NoahPerkovich/pi-pico-mag/operate/sdcard.py

"""
MicroPython driver for SD cards using SPI bus.

Requires an SPI bus and a CS pin.  Provides readblocks and writeblocks
methods so the device can be mounted as a filesystem.

Example usage on pyboard:

    import pyb, sdcard, os
    sd = sdcard.SDCard(pyb.SPI(1), pyb.Pin.board.X5)
    pyb.mount(sd, '/sd2')
    os.listdir('/')

Example usage on ESP8266:

    import machine, sdcard, os
    sd = sdcard.SDCard(machine.SPI(1), machine.Pin(15))
    os.mount(sd, '/sd')
    os.listdir('/')

"""

import micropython
from micropython import const
import time
import uctypes

import array

crc7_be_syndrome_table = array.array("B", 0 for x in range(256)) #pre-allocate so it is low in memory

for i, x in enumerate([
	0x00, 0x12, 0x24, 0x36, 0x48, 0x5a, 0x6c, 0x7e,
	0x90, 0x82, 0xb4, 0xa6, 0xd8, 0xca, 0xfc, 0xee,
	0x32, 0x20, 0x16, 0x04, 0x7a, 0x68, 0x5e, 0x4c,
	0xa2, 0xb0, 0x86, 0x94, 0xea, 0xf8, 0xce, 0xdc,
	0x64, 0x76, 0x40, 0x52, 0x2c, 0x3e, 0x08, 0x1a,
	0xf4, 0xe6, 0xd0, 0xc2, 0xbc, 0xae, 0x98, 0x8a,
	0x56, 0x44, 0x72, 0x60, 0x1e, 0x0c, 0x3a, 0x28,
	0xc6, 0xd4, 0xe2, 0xf0, 0x8e, 0x9c, 0xaa, 0xb8,
	0xc8, 0xda, 0xec, 0xfe, 0x80, 0x92, 0xa4, 0xb6,
	0x58, 0x4a, 0x7c, 0x6e, 0x10, 0x02, 0x34, 0x26,
	0xfa, 0xe8, 0xde, 0xcc, 0xb2, 0xa0, 0x96, 0x84,
	0x6a, 0x78, 0x4e, 0x5c, 0x22, 0x30, 0x06, 0x14,
	0xac, 0xbe, 0x88, 0x9a, 0xe4, 0xf6, 0xc0, 0xd2,
	0x3c, 0x2e, 0x18, 0x0a, 0x74, 0x66, 0x50, 0x42,
	0x9e, 0x8c, 0xba, 0xa8, 0xd6, 0xc4, 0xf2, 0xe0,
	0x0e, 0x1c, 0x2a, 0x38, 0x46, 0x54, 0x62, 0x70,
	0x82, 0x90, 0xa6, 0xb4, 0xca, 0xd8, 0xee, 0xfc,
	0x12, 0x00, 0x36, 0x24, 0x5a, 0x48, 0x7e, 0x6c,
	0xb0, 0xa2, 0x94, 0x86, 0xf8, 0xea, 0xdc, 0xce,
	0x20, 0x32, 0x04, 0x16, 0x68, 0x7a, 0x4c, 0x5e,
	0xe6, 0xf4, 0xc2, 0xd0, 0xae, 0xbc, 0x8a, 0x98,
	0x76, 0x64, 0x52, 0x40, 0x3e, 0x2c, 0x1a, 0x08,
	0xd4, 0xc6, 0xf0, 0xe2, 0x9c, 0x8e, 0xb8, 0xaa,
	0x44, 0x56, 0x60, 0x72, 0x0c, 0x1e, 0x28, 0x3a,
	0x4a, 0x58, 0x6e, 0x7c, 0x02, 0x10, 0x26, 0x34,
	0xda, 0xc8, 0xfe, 0xec, 0x92, 0x80, 0xb6, 0xa4,
	0x78, 0x6a, 0x5c, 0x4e, 0x30, 0x22, 0x14, 0x06,
	0xe8, 0xfa, 0xcc, 0xde, 0xa0, 0xb2, 0x84, 0x96,
	0x2e, 0x3c, 0x0a, 0x18, 0x66, 0x74, 0x42, 0x50,
	0xbe, 0xac, 0x9a, 0x88, 0xf6, 0xe4, 0xd2, 0xc0,
	0x1c, 0x0e, 0x38, 0x2a, 0x54, 0x46, 0x70, 0x62,
	0x8c, 0x9e, 0xa8, 0xba, 0xc4, 0xd6, 0xe0, 0xf2
]):
    crc7_be_syndrome_table[i] = x #fill pre-allocated table


import gc
gc.collect() #make sure residual list gets cleaned up to save memory

@micropython.viper
def crc7(buf, n:int) -> int:
    table = ptr8(uctypes.addressof(crc7_be_syndrome_table))
    bp = ptr8(uctypes.addressof(buf))
    idx = 0
    crc = 0
    while idx < n:
        crc = table[crc ^ bp[idx]]
        idx  = idx + 1  
    return crc

_CMD_TIMEOUT = const(50)

_R1_IDLE_STATE = const(1 << 0)
# R1_ERASE_RESET = const(1 << 1)
_R1_ILLEGAL_COMMAND = const(1 << 2)
# R1_COM_CRC_ERROR = const(1 << 3)
# R1_ERASE_SEQUENCE_ERROR = const(1 << 4)
# R1_ADDRESS_ERROR = const(1 << 5)
# R1_PARAMETER_ERROR = const(1 << 6)
_TOKEN_CMD25 = const(0xFC)
_TOKEN_STOP_TRAN = const(0xFD)
_TOKEN_DATA = const(0xFE)


class SDCard:
    def __init__(self, spi, cs, baudrate=1320000):
        self.spi = spi
        self.cs = cs

        self.cmdbuf = bytearray(6)
        self.dummybuf = bytearray(512)
        self.tokenbuf = bytearray(1)
        for i in range(512):
            self.dummybuf[i] = 0xFF
        self.dummybuf_memoryview = memoryview(self.dummybuf)

        # initialise the card
        self.init_card(baudrate)

    def init_spi(self, baudrate):
        try:
            master = self.spi.MASTER
        except AttributeError:
            # on ESP8266
            self.spi.init(baudrate=baudrate, phase=0, polarity=0)
        else:
            # on pyboard
            self.spi.init(master, baudrate=baudrate, phase=0, polarity=0)

    def init_card(self, baudrate):
        # init CS pin
        self.cs.init(self.cs.OUT, value=1)

        # init SPI bus; use low data rate for initialisation
        self.init_spi(100000)

        # clock card at least 100 cycles with cs high
        for i in range(16):
            self.spi.write(b"\xff")

        # CMD0: init card; should return _R1_IDLE_STATE (allow 5 attempts)
        for _ in range(5):
            if self.cmd(0, 0, 0x95) == _R1_IDLE_STATE:
                break
        else:
            raise OSError("no SD card")

        # CMD8: determine card version
        r = self.cmd(8, 0x01AA, 0x87, 4)
        if r == _R1_IDLE_STATE:
            self.init_card_v2()
        elif r == (_R1_IDLE_STATE | _R1_ILLEGAL_COMMAND):
            self.init_card_v1()
        else:
            raise OSError("couldn't determine SD card version")

        # get the number of sectors
        # CMD9: response R2 (R1 byte + 16-byte block read)
        if self.cmd(9, 0, 0, 0, False) != 0:
            raise OSError("no response from SD card")
        csd = bytearray(16)
        self.readinto(csd)
        if csd[0] & 0xC0 == 0x40:  # CSD version 2.0
            self.sectors = ((csd[8] << 8 | csd[9]) + 1) * 1024
        elif csd[0] & 0xC0 == 0x00:  # CSD version 1.0 (old, <=2GB)
            c_size = (csd[6] & 0b11) << 10 | csd[7] << 2 | csd[8] >> 6
            c_size_mult = (csd[9] & 0b11) << 1 | csd[10] >> 7
            read_bl_len = csd[5] & 0b1111
            capacity = (c_size + 1) * (2 ** (c_size_mult + 2)) * (2**read_bl_len)
            self.sectors = capacity // 512
        else:
            raise OSError("SD card CSD format not supported")
        # print('sectors', self.sectors)

        # CMD16: set block length to 512 bytes
        if self.cmd(16, 512, 0) != 0:
            raise OSError("can't set 512 block size")

        # set to high data rate now that it's initialised
        self.init_spi(baudrate)

    def init_card_v1(self):
        for i in range(_CMD_TIMEOUT):
            time.sleep_ms(50)
            self.cmd(55, 0, 0)
            if self.cmd(41, 0, 0) == 0:
                # SDSC card, uses byte addressing in read/write/erase commands
                self.cdv = 512
                # print("[SDCard] v1 card")
                return
        raise OSError("timeout waiting for v1 card")

    def init_card_v2(self):
        for i in range(_CMD_TIMEOUT):
            self.cmd(55, 0, 0)
            time.sleep_ms(50)
            if (res := self.cmd(41, 0x40000000, 0)) == 0:
                self.cmd(58, 0, 0, -4)  # 4-byte response, negative means keep the first byte
                ocr = self.tokenbuf[0]  # get first byte of response, which is OCR
                if not ocr & 0x40:
                    # SDSC card, uses byte addressing in read/write/erase commands
                    self.cdv = 512
                else:
                    # SDHC/SDXC card, uses block addressing in read/write/erase commands
                    self.cdv = 1
                # print("[SDCard] v2 card")
                return
                
        raise OSError("timeout waiting for v2 card")

    def cmd(self, cmd, arg, crc, final=0, release=True, skip1=False):
        self.cs(0)
        w = self.spi.write #prebind
        r = self.spi.readinto
        
        # create and send the command
        buf = self.cmdbuf
        buf[0] = 0x40 | cmd
        buf[1] = arg >> 24
        buf[2] = arg >> 16
        buf[3] = arg >> 8
        buf[4] = arg
        buf[5] = crc7(buf, 5) | 1  
        w(buf)

        if skip1:
            r(self.tokenbuf, 0xFF)

        # wait for the response (response[7] == 0)
        for i in range(_CMD_TIMEOUT):
            r(self.tokenbuf, 0xFF)
            response = self.tokenbuf[0]
            #print(f"response: {response:02x}")
            
            if not (response & 0x80):
                # this could be a big-endian integer that we are getting here
                # if final<0 then store the first byte to tokenbuf and discard the rest
                if final < 0:
                    r(self.tokenbuf, 0xFF)
                    final = -1 - final
                for j in range(final):
                    w(b"\xff")
                if release:
                    self.cs(1)
                    w(b"\xff")
                return response

        # timeout
        self.cs(1)
        w(b"\xff")
        return -1

    def readinto(self, buf):
        self.cs(0)

        # read until start byte (0xff)
        for i in range(_CMD_TIMEOUT):
            self.spi.readinto(self.tokenbuf, 0xFF)
            if self.tokenbuf[0] == _TOKEN_DATA:
                break
        else:
            self.cs(1)
            raise OSError("timeout waiting for response")

        # read data
        mv = self.dummybuf_memoryview
        if len(buf) != len(mv):
            mv = mv[: len(buf)]
        self.spi.write_readinto(mv, buf)

        # read checksum
        self.spi.write(b"\xff")
        self.spi.write(b"\xff")

        self.cs(1)
        self.spi.write(b"\xff")

    def write(self, token, buf):
        self.cs(0)

        # send: start of block, data, checksum
        self.spi.read(1, token)
        self.spi.write(buf)
        self.spi.write(b"\xff")
        self.spi.write(b"\xff")

        # check the response
        if (self.spi.read(1, 0xFF)[0] & 0x1F) != 0x05:
            self.cs(1)
            self.spi.write(b"\xff")
            return

        # wait for write to finish
        while self.spi.read(1, 0xFF)[0] == 0:
            pass

        self.cs(1)
        self.spi.write(b"\xff")

    def write_token(self, token):
        self.cs(0)
        self.spi.read(1, token)
        self.spi.write(b"\xff")
        # wait for write to finish
        while self.spi.read(1, 0xFF)[0] == 0x00:
            pass

        self.cs(1)
        self.spi.write(b"\xff")

    def readblocks(self, block_num, buf):
        # workaround for shared bus, required for (at least) some Kingston
        # devices, ensure MOSI is high before starting transaction
        self.spi.write(b"\xff")

        nblocks = len(buf) // 512
        assert nblocks and not len(buf) % 512, "Buffer length is invalid"
        if nblocks == 1:
            # CMD17: set read address for single block
            if self.cmd(17, block_num * self.cdv, 0, release=False) != 0:
                # release the card
                self.cs(1)
                raise OSError(5)  # EIO
            # receive the data and release card
            self.readinto(buf)
        else:
            # CMD18: set read address for multiple blocks
            if self.cmd(18, block_num * self.cdv, 0, release=False) != 0:
                # release the card
                self.cs(1)
                raise OSError(5)  # EIO
            offset = 0
            mv = memoryview(buf)
            while nblocks:
                # receive the data and release card
                self.readinto(mv[offset : offset + 512])
                offset += 512
                nblocks -= 1
            if self.cmd(12, 0, 0xFF, skip1=True):
                raise OSError(5)  # EIO

    def writeblocks(self, block_num, buf):
        # workaround for shared bus, required for (at least) some Kingston
        # devices, ensure MOSI is high before starting transaction
        self.spi.write(b"\xff")

        nblocks, err = divmod(len(buf), 512)
        assert nblocks and not err, "Buffer length is invalid"
        if nblocks == 1:
            # CMD24: set write address for single block
            if self.cmd(24, block_num * self.cdv, 0) != 0:
                raise OSError(5)  # EIO

            # send the data
            self.write(_TOKEN_DATA, buf)
        else:
            # CMD25: set write address for first block
            if self.cmd(25, block_num * self.cdv, 0) != 0:
                raise OSError(5)  # EIO
            # send the data
            offset = 0
            mv = memoryview(buf)
            while nblocks:
                self.write(_TOKEN_CMD25, mv[offset : offset + 512])
                offset += 512
                nblocks -= 1
            self.write_token(_TOKEN_STOP_TRAN)

    def ioctl(self, op, arg):
        if op == 4:  # get number of blocks
            return self.sectors
        if op == 5:  # get block size in bytes
            return 512
